Brunoarico/centrifuge/centrifuge_codes/game.h

#include <stdio.h>
const int NGLYPHS = 6;

byte glyphs[NGLYPHS][8] = {
  // 1: car up
  { B00000,
    B01110,
    B11111,
    B01010,
    B00000,
    B00000,
    B00000,
    B00000}
  // 2: car down
  ,{B00000,
    B00000,
    B00000,
    B00000,
    B01110,
    B11111,
    B01010,
    B00000}
  // 3: truck up
  ,{B00000,
    B11110,
    B11111,
    B01010,
    B00000,
    B00000,
    B00000,
    B00000}
  // 4: truck down
  ,{B00000,
    B00000,
    B00000,
    B00000,
    B11110,
    B11111,
    B01010,
    B00000}
  // 5: crash up
  ,{B10101,
    B01110,
    B01110,
    B10101,
    B00000,
    B00000,
    B00000,
    B00000}
  // 6: crash down
  ,{B00000,
    B00000,
    B00000,
    B10101,
    B01110,
    B01110,
    B10101,
    B00000}
};

const int NCARPOSITIONS = 4;

const char BLANK=32;
char car2glyphs[NCARPOSITIONS][2] = {
  {1,BLANK},{2,BLANK},{BLANK,1},{BLANK,2}
};
char truck2glyphs[NCARPOSITIONS][2] = {
  {3,BLANK},{4,BLANK},{BLANK,3},{BLANK,4}
};
char crash2glyphs[NCARPOSITIONS][2] = {
  {5,BLANK},{6,BLANK},{BLANK,5},{BLANK,6}
};
const int MAXSTEPDURATION = 300; // Start slowly, each step is 1 millisec shorter.
const int MINSTEPDURATION = 150; // This is as fast as it gets
const int ROADLEN = 15; // LCD width (not counting our car)
int road[ROADLEN]; // positions of other cars
char line_buff[2+ROADLEN]; // aux string for drawRoad()
int road_index;
int factor = 4;
int car_pos;
// Off-the-grid position means empty column, so MAXROADPOS
// determines the probability of a car in a column
// e.g. 3*NCARPOSITIONS gives p=1/3
const int MAXROADPOS = 3*NCARPOSITIONS;
int step_duration;

bool crash; // true if crashed
unsigned long int crashtime; // millis() when crashed
unsigned long int begintime;
const int CRASHSOUNDDURATION = 250;
